svenscore/vecdec/stl/1.1/tray left.stl

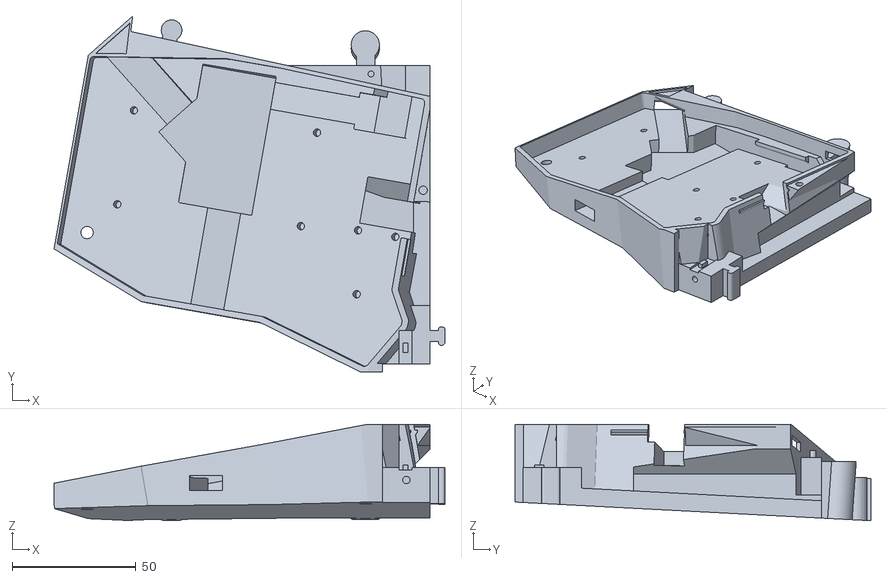
[picture p26: CAD file, 2025-08-03]
stl/1.1/tray left.stl
157.7 x 143.6 x 38.9
