svenscore/vecdec/stl/1.0/screen backplate.stl

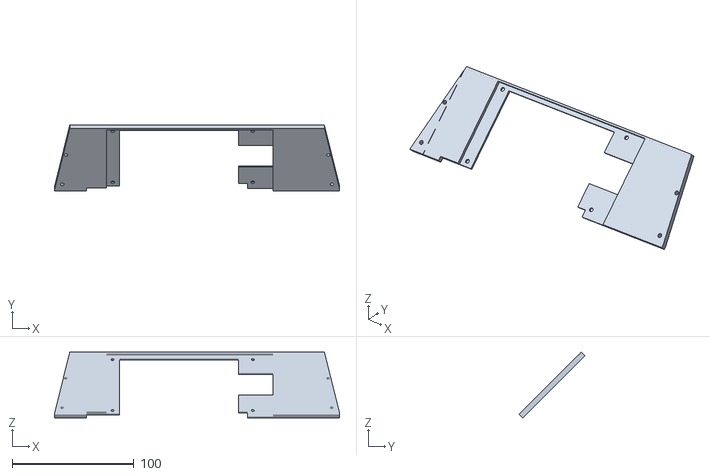
[picture p27: CAD file, 2024-08-19]
stl/1.0/screen backplate.stl
233.8 x 54.1 x 54.1
