svenscore/vecdec/stl/1.1/tray center trackball.stl

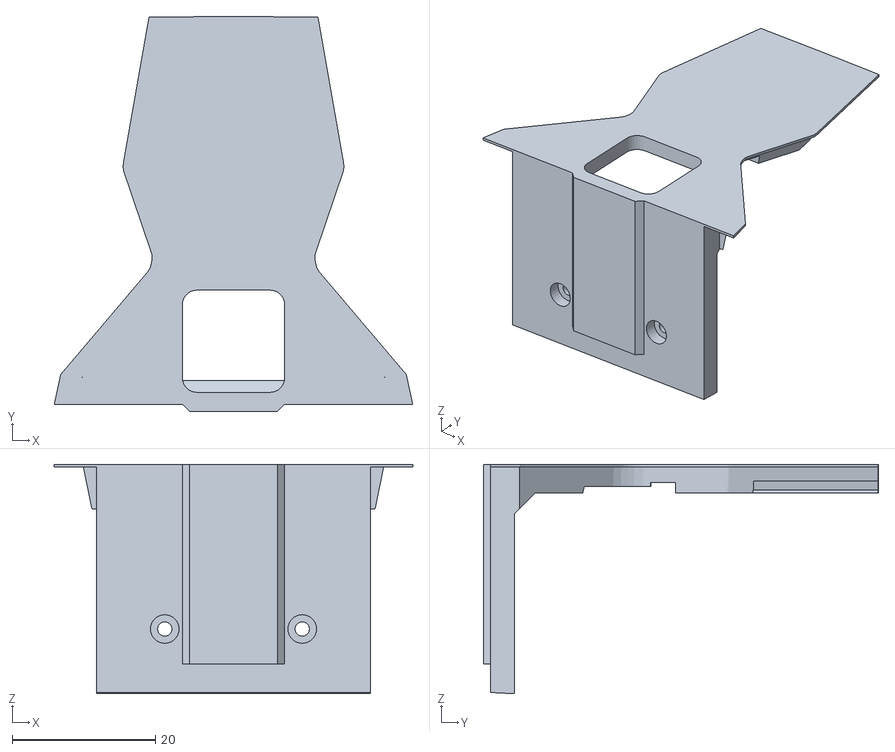
[picture p28: CAD file, 2025-08-03]
stl/1.1/tray center trackball.stl
50.0 x 55.1 x 32.0
