svenscore/vecdec/stl/1.0/shell sx1262.stl

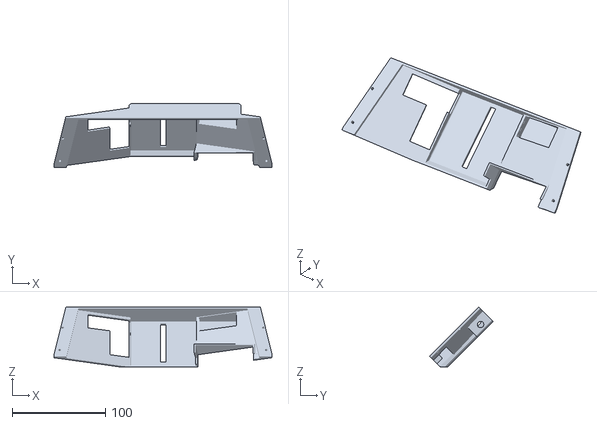
[picture p29: CAD file, 2024-08-19]
stl/1.0/shell sx1262.stl
233.8 x 68.2 x 64.0
