svenscore/vecdec/stl/1.1/tray right.stl

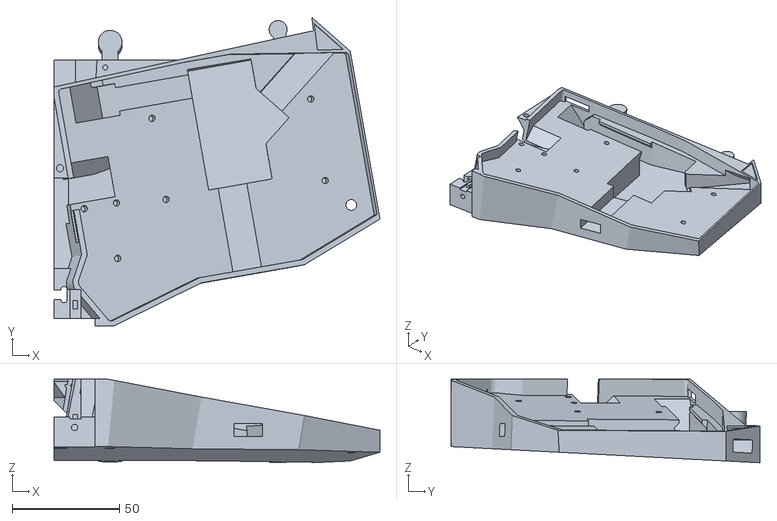
[picture p30: CAD file, 2025-08-03]
stl/1.1/tray right.stl
151.8 x 143.6 x 38.9
