svenscore/vecdec/stl/1.0/tray left veneer.stl

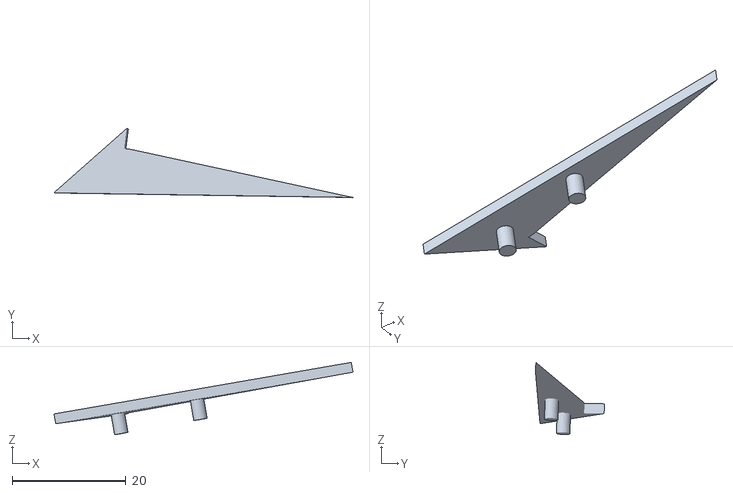
[picture p31: CAD file, 2024-08-19]
stl/1.0/tray left veneer.stl
52.7 x 12.2 x 12.7
