svenscore/vecdec/stl/1.1/case 2 1280x800.stl

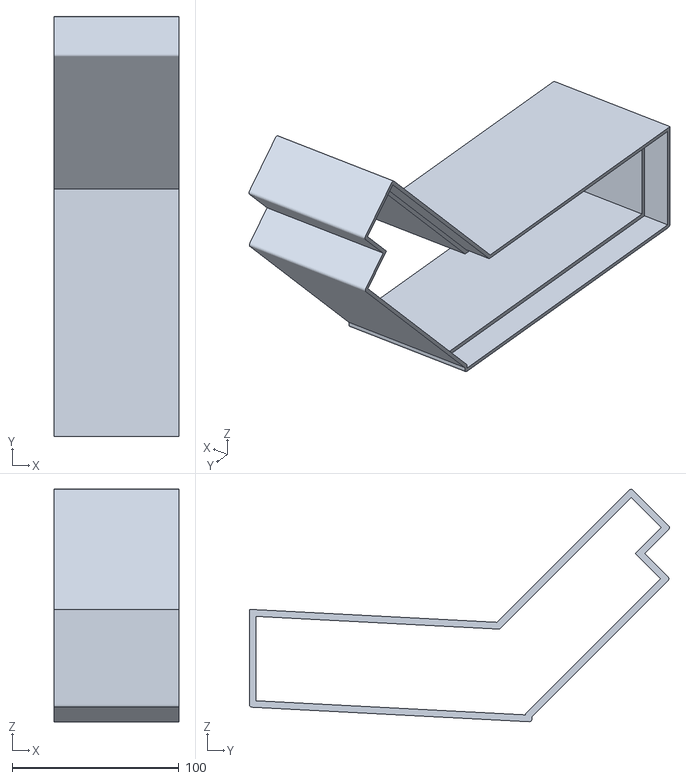
[picture p32: CAD file, 2025-08-03]
stl/1.1/case 2 1280x800.stl
74.9 x 251.9 x 139.5
