svenscore/vecdec/stl/1.1/sofle top plate.stl

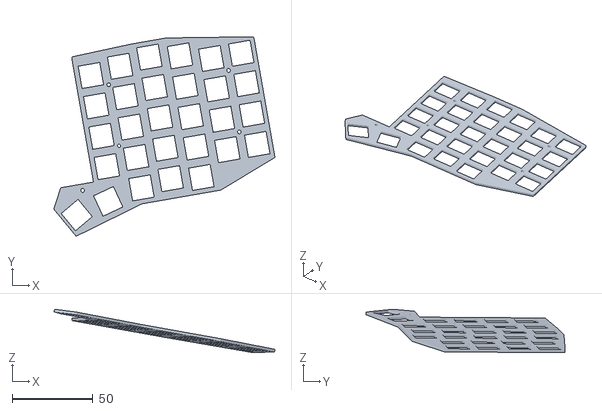
[picture p33: CAD file, 2025-08-03]
stl/1.1/sofle top plate.stl
136.4 x 123.1 x 26.8
