svenscore/vecdec/stl/1.1/screen backplate 1280x800.stl

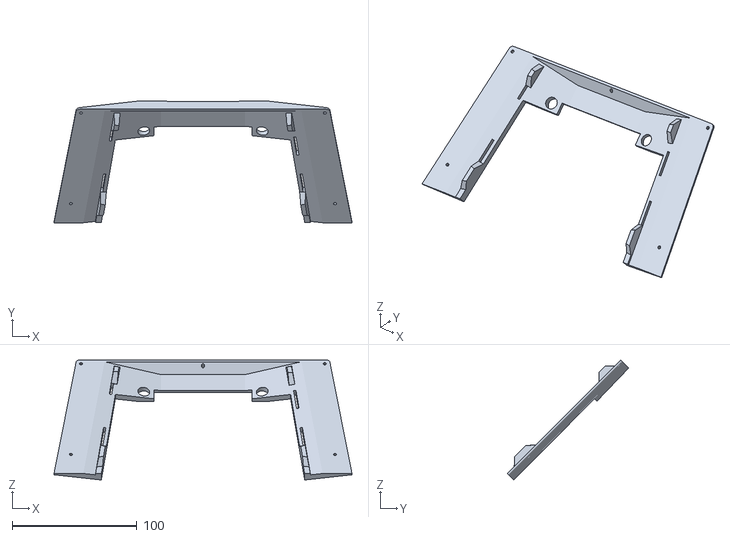
[picture p34: CAD file, 2025-08-03]
stl/1.1/screen backplate 1280x800.stl
239.0 x 97.5 x 96.2
