svenscore/vecdec/kicad/qwiic_sao/qwiic_sao.kicad_sch

## KiCad design kicad/qwiic_sao/qwiic_sao.kicad_sch (2025-08-03)

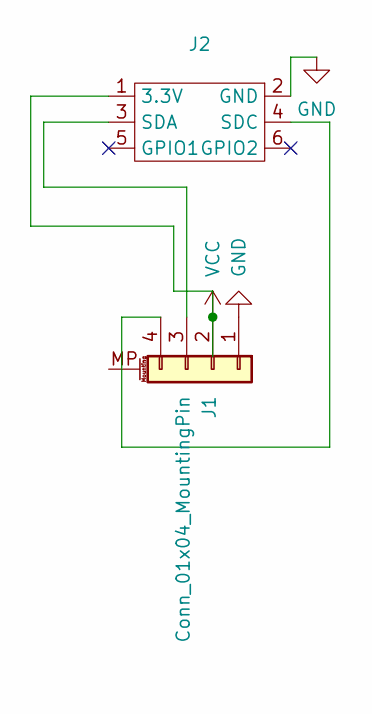
[picture p35: schematic qwiic_sao.kicad_sch]

Parts:
J1: Conn_01x04_MountingPin; CONN_PRT-14417_SPK
J2: Simple_Addon_v2-BADGE-2x3

Connections:
GND: J1.1, J2.2 (GND)
unnamed: J1.3, J2.3 (SDA)
unnamed: J1.4, J2.4 (SDC)
VCC: J1.2, J2.1 (3.3V)
